anafedeles/TSC_EBookReader_Project/Images/baterie.png

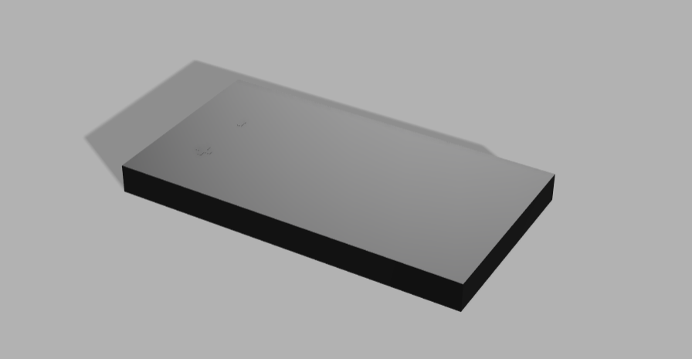
Images/baterie.png
