anafedeles/TSC_EBookReader_Project/Images/display2.jpg

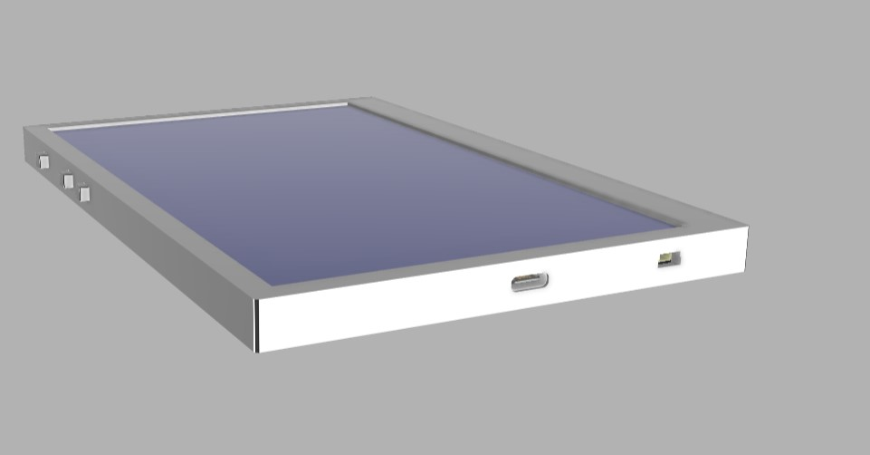
Images/display2.jpg
