anafedeles/TSC_EBookReader_Project/Images/display.jpg

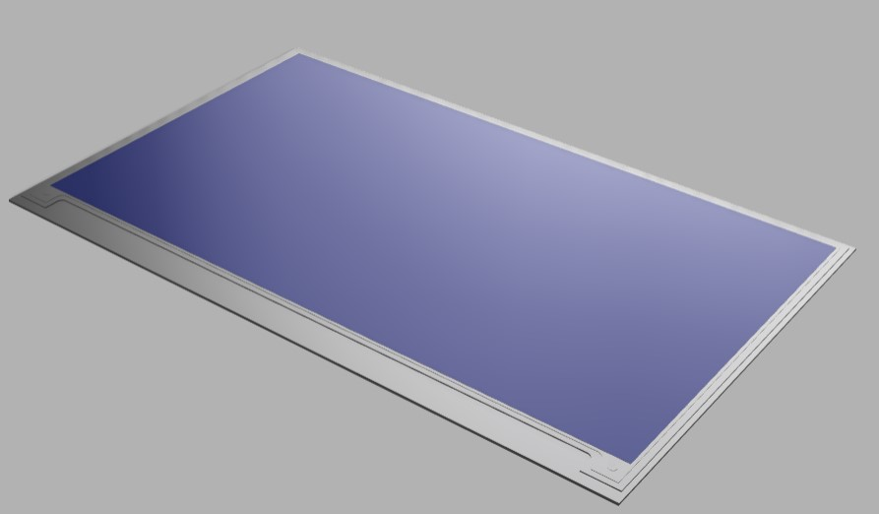
Images/display.jpg
