anafedeles/TSC_EBookReader_Project/Images/display.png

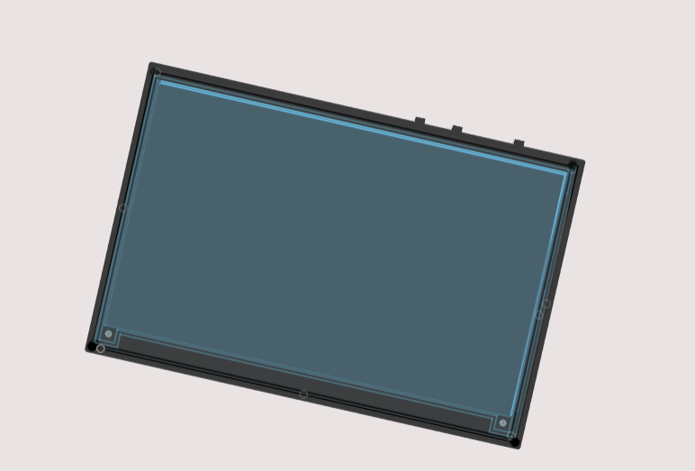
Images/display.png
