anafedeles/TSC_EBookReader_Project/Images/OpenBook_PCB_2025-Apr-14_10-53-12PM-000_CustomizedView39760220098.jpg

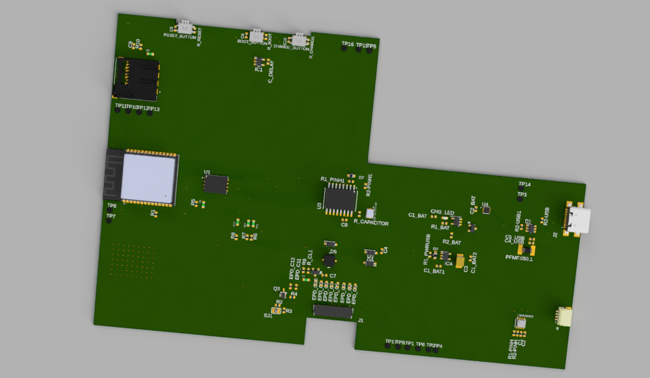
Images/OpenBook_PCB_2025-Apr-14_10-53-12PM-000_CustomizedView39760220098.jpg
