anafedeles/TSC_EBookReader_Project/Images/OpenBook_PCB_2025-Apr-14_10-55-13PM-000_CustomizedView21744814541.jpg

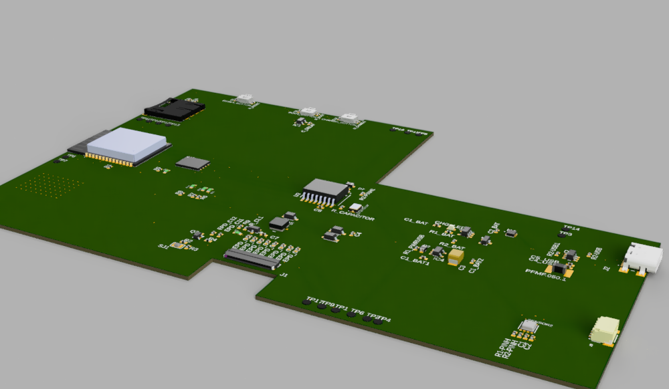
Images/OpenBook_PCB_2025-Apr-14_10-55-13PM-000_CustomizedView21744814541.jpg
